achurichi/nanobot/ros/nanobot_diffdrive/hardware/include/nanobot_diffdrive/nanobot_system.hpp

#ifndef NANOBOT_DIFFDRIVE__NANOBOT_SYSTEM_HPP_
#define NANOBOT_DIFFDRIVE__NANOBOT_SYSTEM_HPP_

#include <memory>
#include <string>
#include <vector>

#include "hardware_interface/handle.hpp"
#include "hardware_interface/hardware_info.hpp"
#include "hardware_interface/system_interface.hpp"
#include "hardware_interface/types/hardware_interface_return_values.hpp"
#include "rclcpp/clock.hpp"
#include "rclcpp/duration.hpp"
#include "rclcpp/macros.hpp"
#include "rclcpp/time.hpp"
#include "rclcpp_lifecycle/node_interfaces/lifecycle_node_interface.hpp"
#include "rclcpp_lifecycle/state.hpp"

#include "nanobot_diffdrive/dynamixel_comms.hpp"
#include "nanobot_diffdrive/wheel.hpp"

namespace nanobot_diffdrive
{
  class NanobotDiffDriveHardware : public hardware_interface::SystemInterface
  {
    struct Config
    {
      int velocity_limit = 0;
      float rpm_per_unit = 0.0;
      float deg_per_pulse = 0.0;
      std::string device = "";
      float protocol_version = 0.0;
      int baud_rate = 0;
    };

    struct ConfiguredWheel {
      Wheel wheel;
      int motor_id;
      double sign;
    };

  public:
    RCLCPP_SHARED_PTR_DEFINITIONS(NanobotDiffDriveHardware)

    hardware_interface::CallbackReturn on_init(
        const hardware_interface::HardwareInfo &info) override;

    std::vector<hardware_interface::StateInterface> export_state_interfaces() override;

    std::vector<hardware_interface::CommandInterface> export_command_interfaces() override;

    hardware_interface::CallbackReturn on_configure(
        const rclcpp_lifecycle::State &previous_state) override;

    hardware_interface::CallbackReturn on_cleanup(
        const rclcpp_lifecycle::State &previous_state) override;

    hardware_interface::CallbackReturn on_activate(
        const rclcpp_lifecycle::State &previous_state) override;

    hardware_interface::CallbackReturn on_deactivate(
        const rclcpp_lifecycle::State &previous_state) override;

    hardware_interface::return_type read(
        const rclcpp::Time &time, const rclcpp::Duration &period) override;

    hardware_interface::return_type write(
        const rclcpp::Time &time, const rclcpp::Duration &period) override;

  private:
    DynamixelComms comms_;
    Config cfg_;
    std::vector<ConfiguredWheel> wheels_;
  };

} // namespace nanobot_diffdrive

#endif // NANOBOT_DIFFDRIVE__NANOBOT_SYSTEM_HPP_
